Nemesis-FT/leoracer/cad files/ArduinoLeonardo.SLDPRT

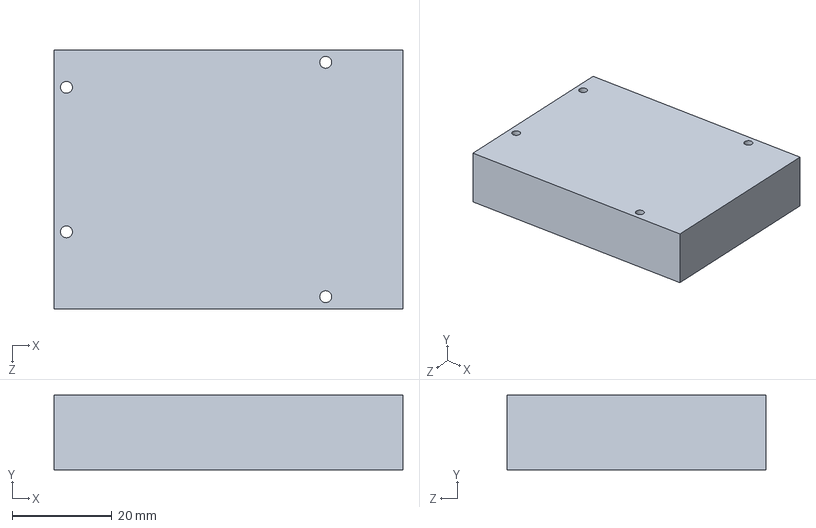
[picture p20: CAD file, 2023-07-12]
cad files/ArduinoLeonardo.SLDPRT
70.0 x 15.0 x 52.0 mm
